bryceehill/LED-Binary-Counter/SWAG_BAR_V0/main.h

/*
 * main.h
 *
 *  Created on: Jun 19, 2023
 *      Author: bhill
 */

#ifndef MAIN_H_
#define MAIN_H_
//#pragma DATA_SECTION(mapArray,".myData");
//#pragma DATA_ALIGN(mapArray,1);
//  #pragma RETAIN(mapArray);
//    __no_init const unsigned char  mapArray[] @ 0xFE00;
const char mapArray[98][5] = {{0,0,0,0,0},      // Space
                              {0,0, 0x7D, 0, 0}, // Exclamation Mark
                              {0,0x60, 0, 0x60, 0}, // double quote
                              {0x14,0x7F,0x14,0x7F,0x14},  //Hash Tag
                              {0x12,0x2A, 0x7F, 0x2A, 0x24},  //$
                              {0x62, 0x64, 0x08, 0x13, 0x23}, //%
                              {0x36, 0x49, 0x35, 0x02, 0x05},   //&
                              {0,0,0x60,0,0},                   //'
                              {0,0,0x3E,0x41,0},                 // (
                              {0,0x41,0x3E,0,0},                // )
                              {0x2A, 0x1C, 0x3E, 0x1C, 0x2A},  // *
                              {0x08,0x08,0x3E, 0x08, 0x08},     // +
                              {0,1,0x06,0,0},                   //,
                              {0,8,8,8,0},                          // -
                              {0,3,3,0,0},                      //.
                              {0x02,0x04,0x08,0x10,0x20},      // /
                              {0x3E, 0x45, 0x49,0x51, 0x3E},  //0
                              {0x00, 0x21, 0x7F, 0x01, 0x00}, // 1
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
                              {0x7F, 0x41, 0x41, 0x41, 0x7F}, // box
                              {0x7F, 0x7F, 0x7F, 0x7F, 0x7F}, // fill box
                              {0,0,0,0,0}};
                                // needs


#endif /* MAIN_H_ */
